bolintw/Kairos/firmware/main/stopwatch_face.cpp

#include "stopwatch_face.hpp"

#include <cstdio>

#include "gui_manager.hpp"

namespace {
// See pomodoro_face.cpp's kColorFocus/kColorBreak for the same convention.
const lv_color_t kColorCountUp = lv_color_make(70, 140, 255);
}  // namespace

void StopwatchFace::onEnter()
{
    elapsed_ms_ = 0;
    running_ = false;
}

void StopwatchFace::onExit()
{
}

void StopwatchFace::onTick(uint32_t dt_ms)
{
    if (running_) {
        elapsed_ms_ += dt_ms;
    }
}

void StopwatchFace::onTap()
{
    running_ = !running_;
}

void StopwatchFace::render(GuiManager& gui)
{
    const uint32_t total_seconds = elapsed_ms_ / 1000;
    const uint32_t hours = total_seconds / 3600;
    const uint32_t minutes = (total_seconds / 60) % 60;
    const uint32_t seconds = total_seconds % 60;

    // Plain libc snprintf, not LVGL's builtin one — the %f-support
    // limitation noted in main.cpp only applies to lv_label_set_text_fmt.
    char buf[16];
    if (hours > 0) {
        std::snprintf(buf, sizeof(buf), "%u:%02u:%02u", static_cast<unsigned int>(hours),
                       static_cast<unsigned int>(minutes), static_cast<unsigned int>(seconds));
    } else {
        std::snprintf(buf, sizeof(buf), "%02u:%02u",
                       static_cast<unsigned int>(minutes), static_cast<unsigned int>(seconds));
    }
    // Resets: opacity/secondary-text state persists across face switches
    // (e.g. mid-fade from PomodoroFace, or a stale phase name from BreathFace).
    gui.SetPrimaryTextOpacity(255);
    gui.SetPrimaryText(buf);
    gui.SetAccentColor(kColorCountUp);
    gui.SetSecondaryText("");
}

TimerFace::Status StopwatchFace::GetStatus() const
{
    // remaining_ms repurposed as "ms elapsed this run" — drives
    // AppController's count-up ring (one hour per revolution).
    return Status{running_, /*has_target=*/false, elapsed_ms_, /*is_break_phase=*/false, /*target_ms=*/0,
                  /*is_count_up=*/true};
}
